OzSecICT/badge-conagotchi/assets/hackachi/Hackachi-BG_V2.png

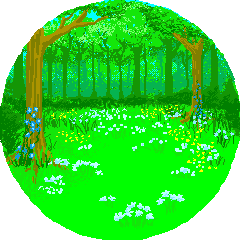
assets/hackachi/Hackachi-BG_V2.png
