OzSecICT/badge-conagotchi/hardware/renders/OzSec2026-ESP32_Black_Gold_back.png

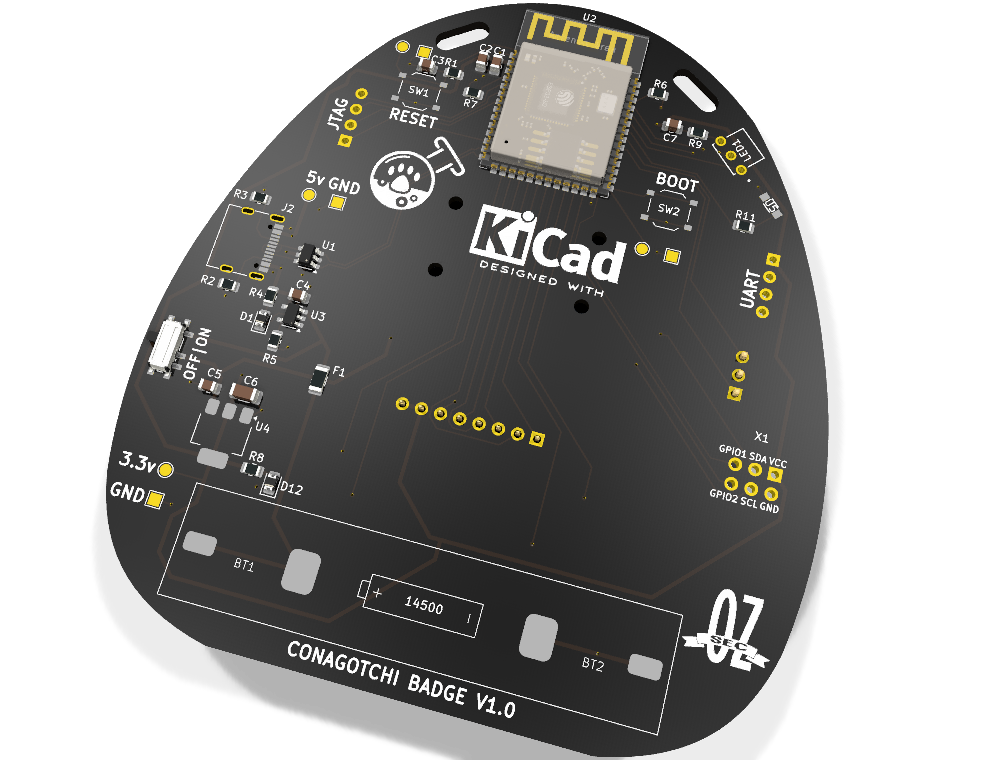
hardware/renders/OzSec2026-ESP32_Black_Gold_back.png
