OzSecICT/badge-conagotchi/hw-test/main/ws2812.h

#pragma once
#include <stdint.h>

void ws2812_init(void);
void ws2812_set(uint8_t idx, uint8_t r, uint8_t g, uint8_t b);
void ws2812_set_all(uint8_t r, uint8_t g, uint8_t b);
void ws2812_clear(void);
void ws2812_show(void);
